nejcokorn/flysys_test/kicad/flysys_vario.kicad_sch

## KiCad design kicad/flysys_vario.kicad_sch (2026-06-08)

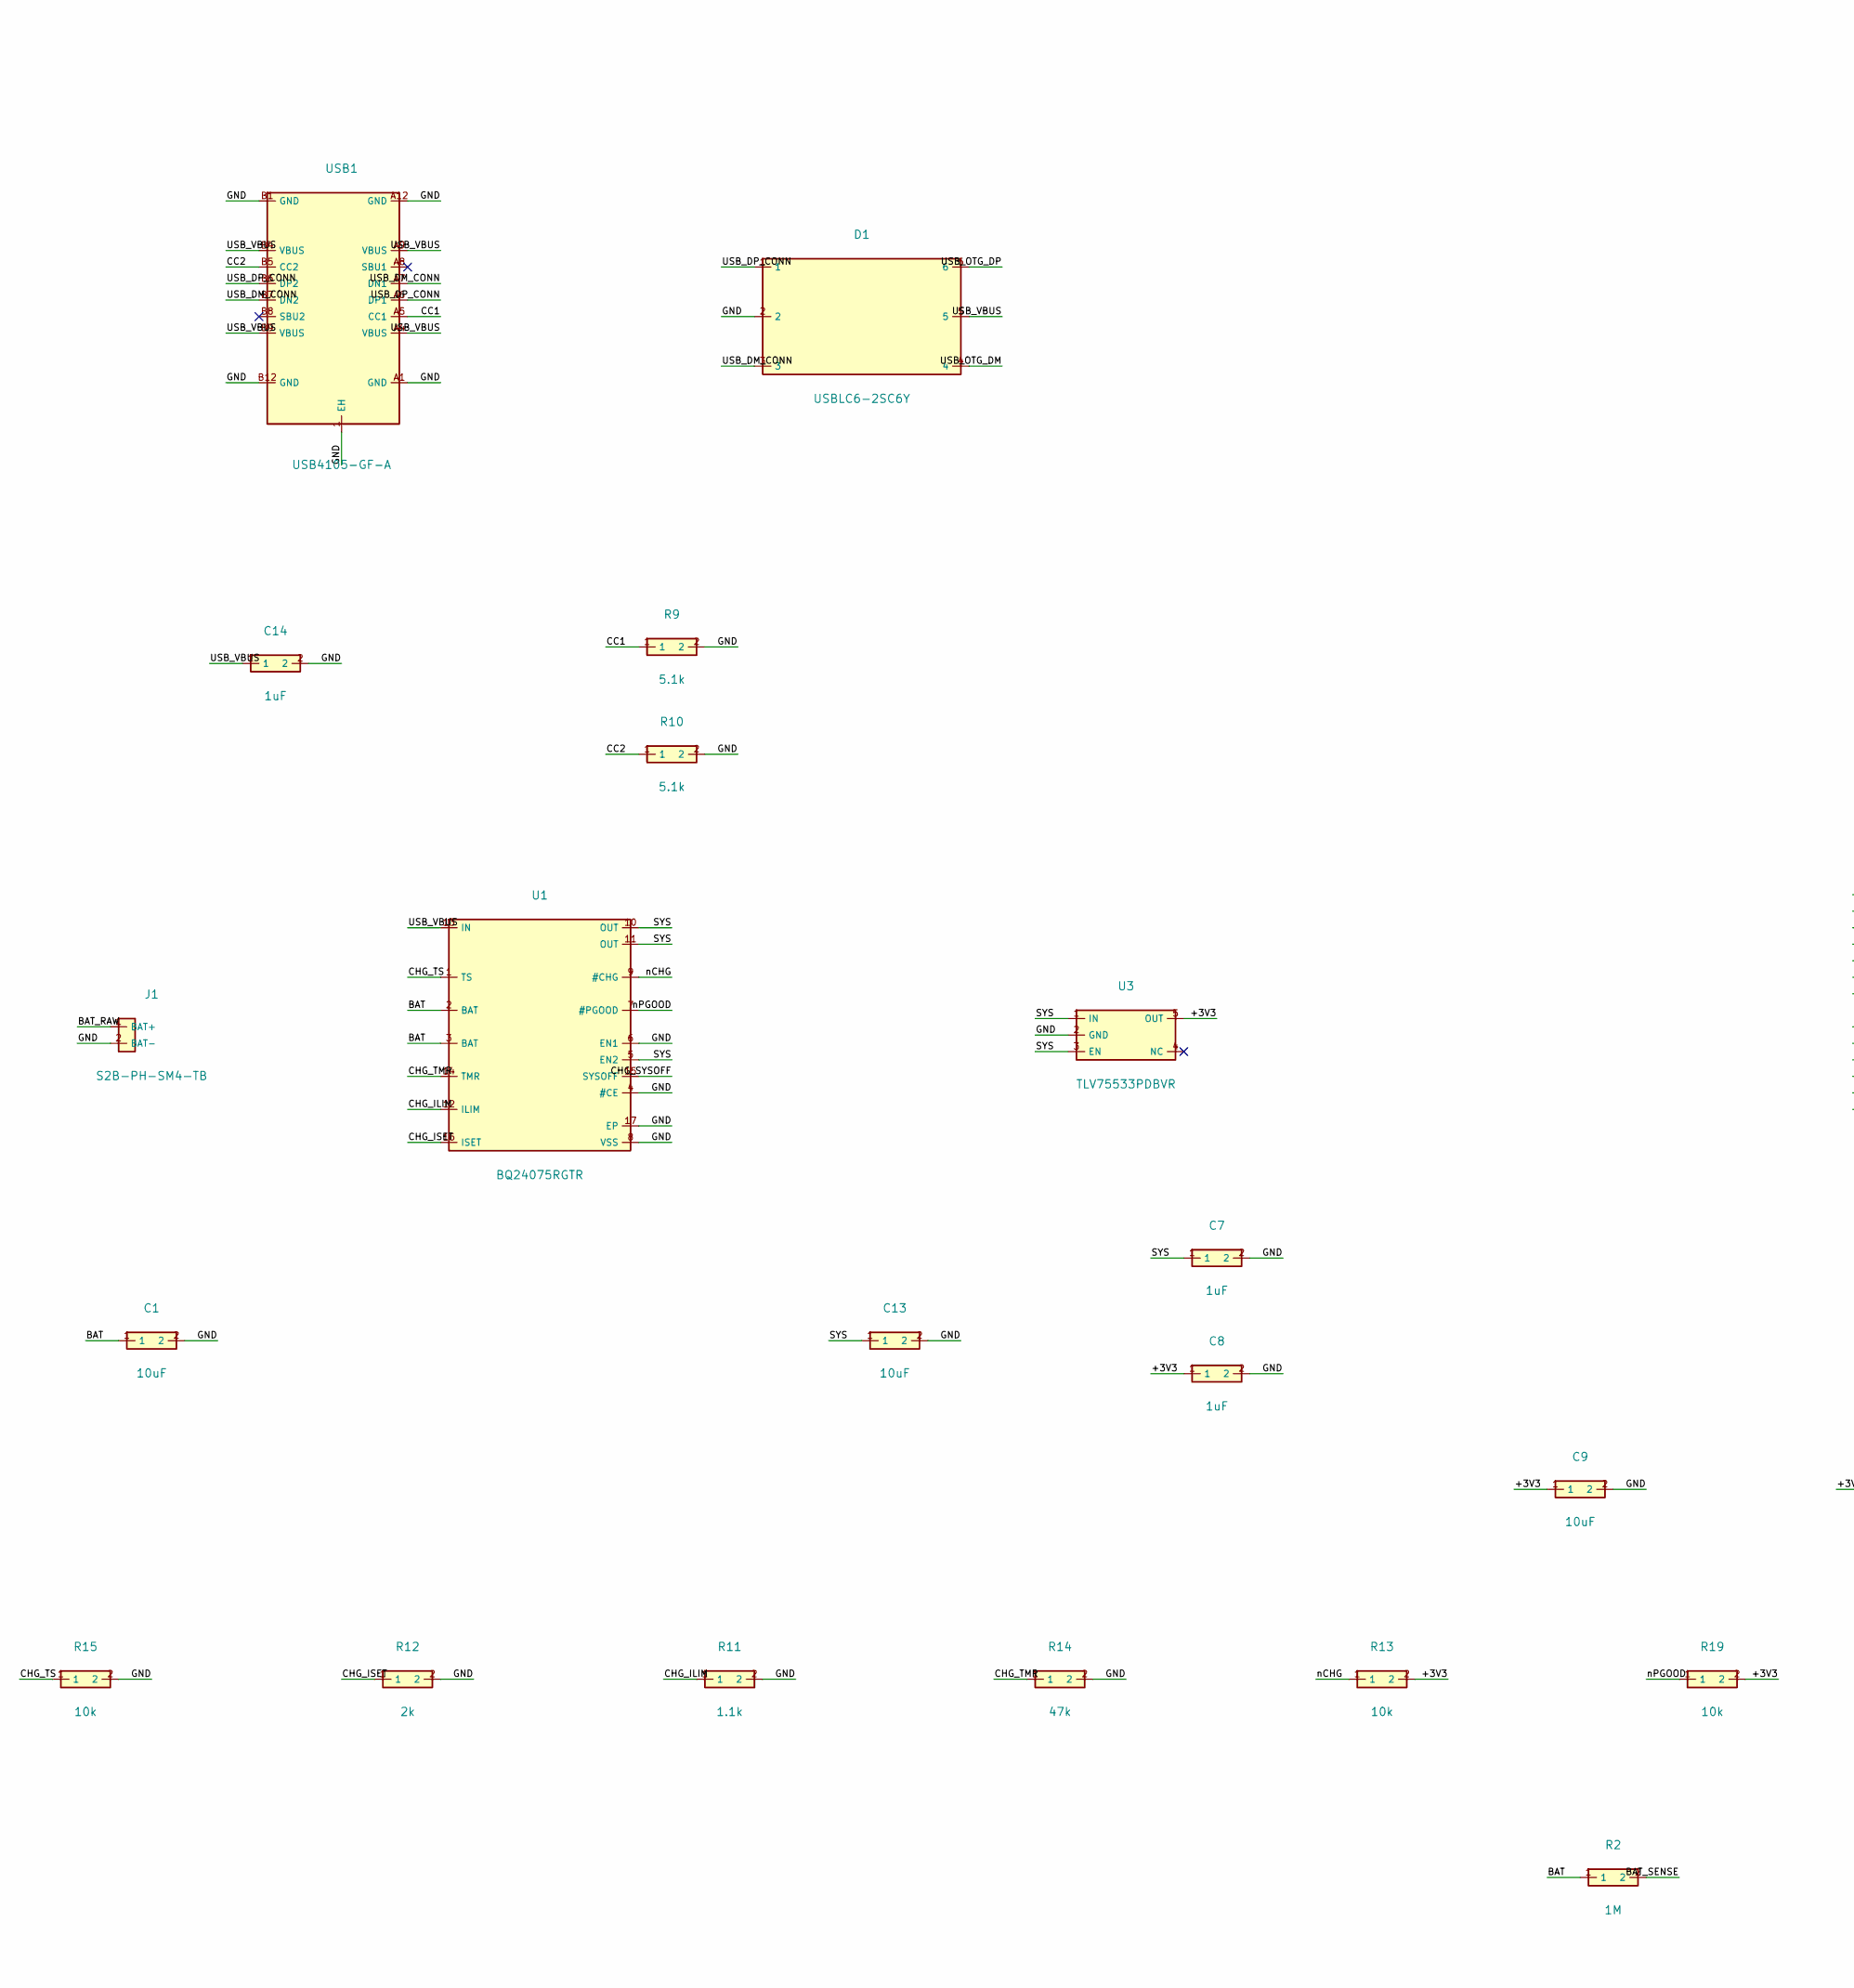
[picture p11: schematic flysys_vario.kicad_sch, part in row 1, column 1]

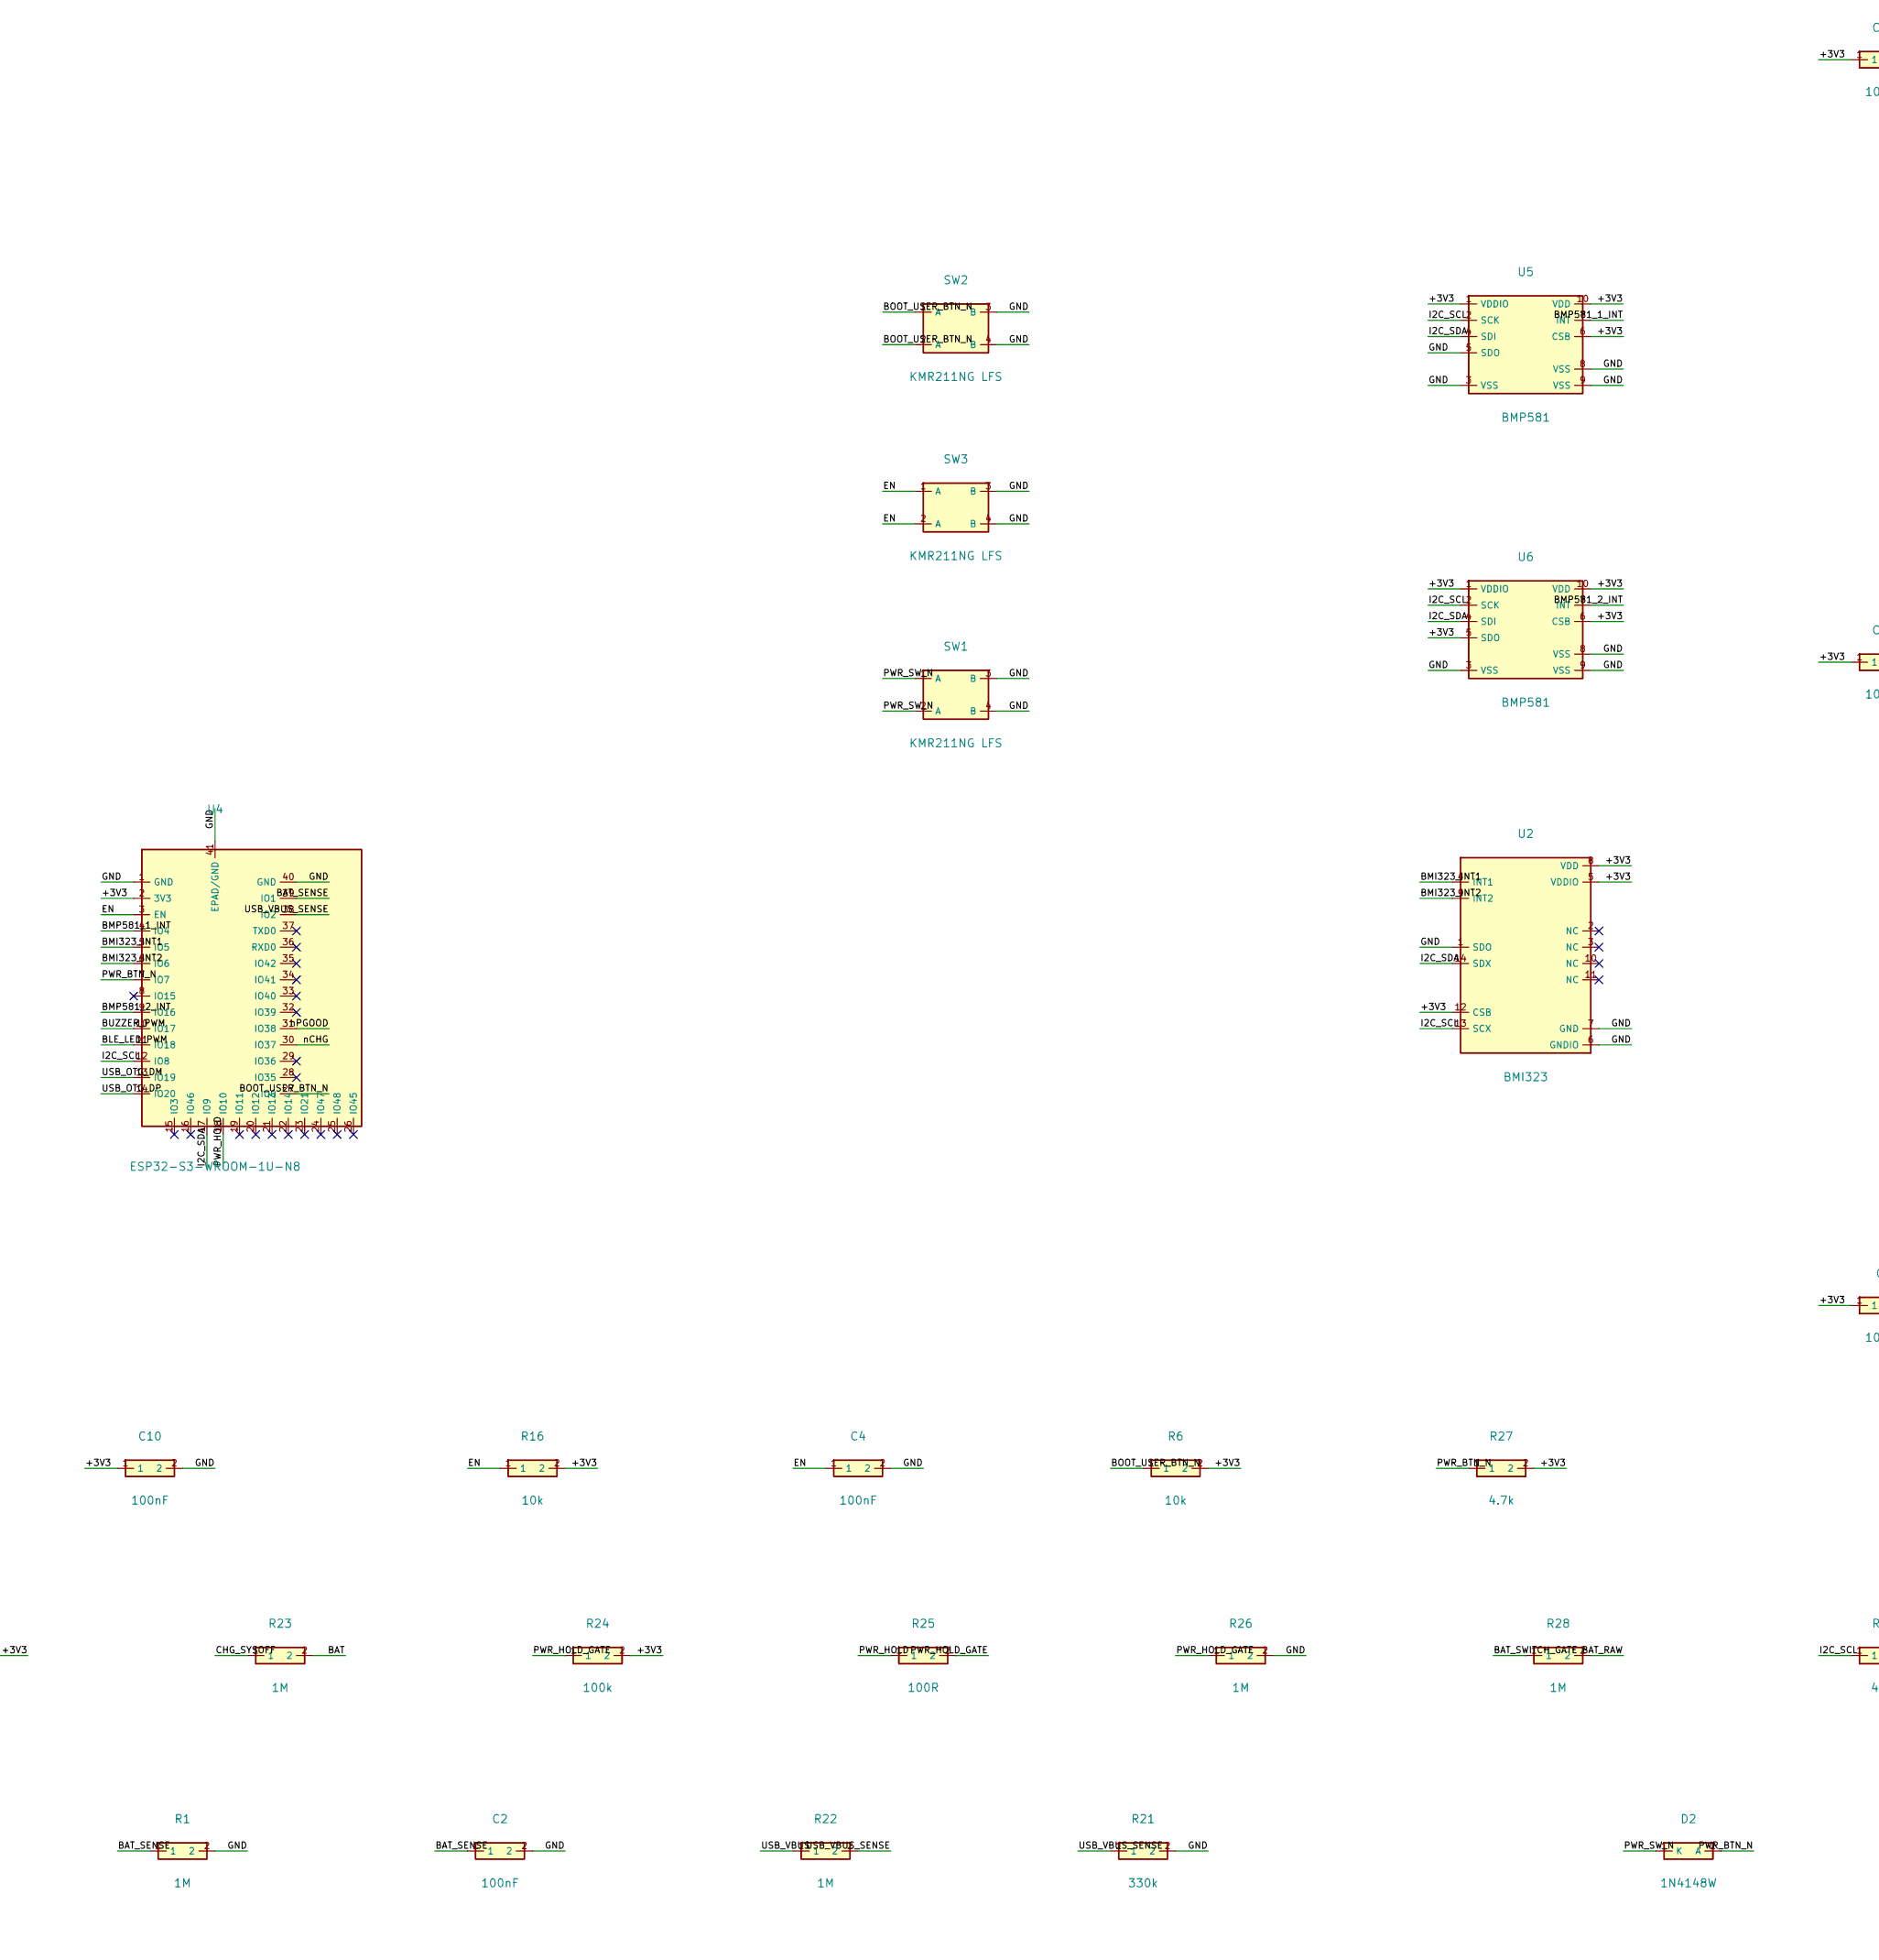
[picture p12: schematic flysys_vario.kicad_sch, part in row 1, column 2]

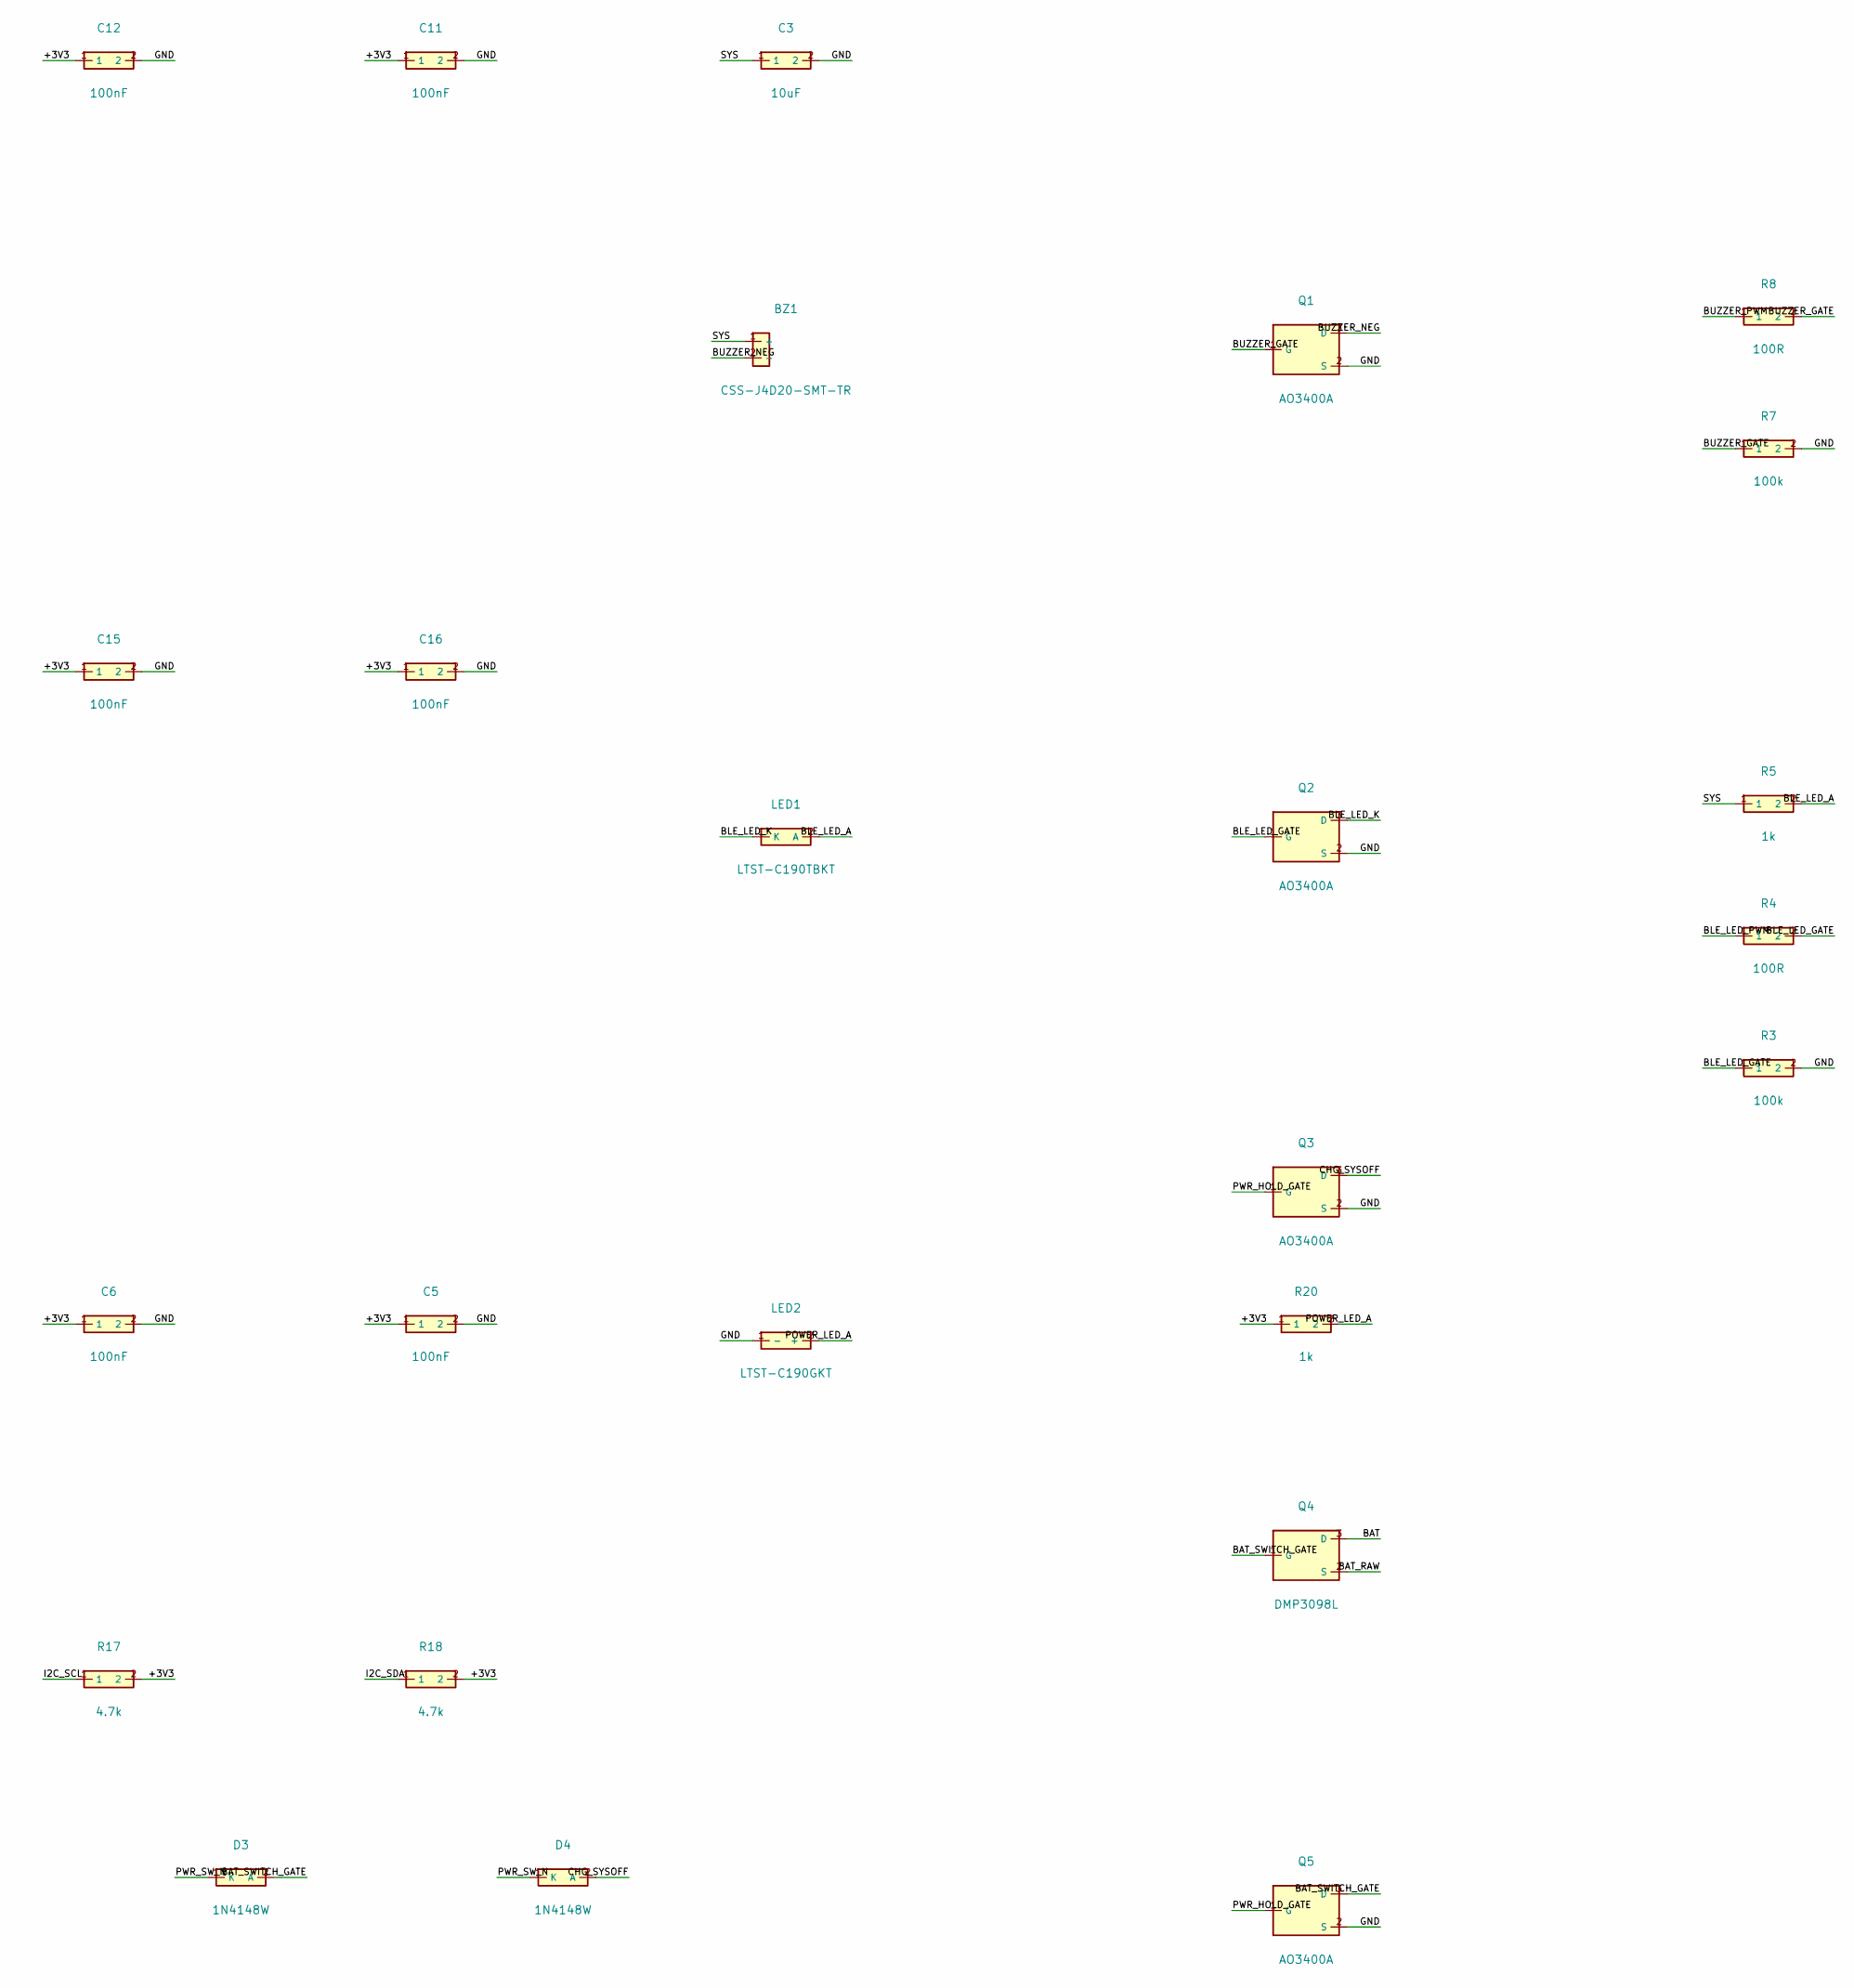
[picture p13: schematic flysys_vario.kicad_sch, part in row 1, column 3]

Parts:
BZ1: CSS-J4D20-SMT-TR; MPN CSS-J4D20-SMT-TR; DigiKey Part Number 102-1198-1-ND
C1, C3, C9, C13: 10uF; C0603; MPN CL10A106KP8NNNC; DigiKey Part Number 1276-1192-1-ND
C2, C4, C5, C6, C10, C11, C12, C15, C16: 100nF; C0603; MPN CC0603KRX7R9BB104; DigiKey Part Number 311-1344-1-ND
C7, C8, C14: 1uF; C0603; MPN CL10A105KB8NNNC; DigiKey Part Number 1276-1860-1-ND
D1: USBLC6-2SC6Y; SOT-23-6_L2.9-W1.6-P0.95-LS2.8-BL; MPN USBLC6-2SC6Y; DigiKey Part Number 497-11882-1-ND
D2, D3, D4: 1N4148W; MPN 1N4148W-7-F; DigiKey Part Number 1N4148W-FDICT-ND
J1: S2B-PH-SM4-TB; MPN S2B-PH-SM4-TB; DigiKey Part Number 455-S2B-PH-SM4-TBCT-ND
LED1: LTST-C190TBKT; LED0603-RD; MPN LTST-C190TBKT; DigiKey Part Number 160-1646-1-ND
LED2: LTST-C190GKT; LED0603-RD; MPN LTST-C190GKT; DigiKey Part Number 160-LTST-C190GKTCT-ND
Q1, Q2, Q3, Q5: AO3400A; MPN AO3400A; DigiKey Part Number 785-1000-1-ND
Q4: DMP3098L; MPN DMP3098L-7; DigiKey Part Number DMP3098LDICT-ND
R1, R2, R22, R23, R26, R28: 1M; R0603; MPN RC0603FR-071ML; DigiKey Part Number 311-1.00MHRCT-ND
R3, R7, R24: 100k; R0603; MPN RC0603FR-07100KL; DigiKey Part Number 311-100KHRCT-ND
R4, R8, R25: 100R; R0603; MPN RC0603FR-07100RL; DigiKey Part Number 311-100HRCT-ND
R5, R20: 1k; R0603; MPN RC0603FR-071KL; DigiKey Part Number 311-1.00KHRCT-ND
R6, R13, R15, R16, R19: 10k; R0603; MPN RC0603FR-0710KL; DigiKey Part Number 311-10.0KHRCT-ND
R9, R10: 5.1k; R0603; MPN RC0603FR-075K1L; DigiKey Part Number 311-5.10KHRCT-ND
R11: 1.1k; R0603; MPN RC0603FR-071K1L; DigiKey Part Number 311-1.10KHRCT-ND
R12: 2k; R0603; MPN RC0603FR-072KL; DigiKey Part Number 311-2.00KHRCT-ND
R14: 47k; R0603; MPN RC0603FR-0747KL; DigiKey Part Number 311-47.0KHRCT-ND
R17, R18, R27: 4.7k; R0603; MPN RC0603FR-074K7L; DigiKey Part Number 311-4.70KHRCT-ND
R21: 330k; R0603; MPN RC0603FR-07330KL; DigiKey Part Number 311-330KHRCT-ND
SW1: KMR211NG LFS; KMR211NG_LFS; MPN KMR211NG LFS; DigiKey Part Number CKN10243CT-ND
SW2: KMR211NG LFS; KMR211NG_LFS_BOOT; MPN KMR211NG LFS; DigiKey Part Number CKN10243CT-ND
SW3: KMR211NG LFS; KMR211NG_LFS_RST; MPN KMR211NG LFS; DigiKey Part Number CKN10243CT-ND
U1: BQ24075RGTR; QFN-16_L3.0-W3.0-P0.50-TL-EP1.7; MPN BQ24075RGTR; DigiKey Part Number 296-38874-1-ND
U2: BMI323; LGA-14_L3.0-W2.5-P0.50-TL_QMI8658A; MPN BMI323; DigiKey Part Number 828-BMI323CT-ND
U3: TLV75533PDBVR; SOT-23-5_L3.0-W1.7-P0.95-LS2.8-BR; MPN TLV75533PDBVR; DigiKey Part Number 296-50411-1-ND
U4: ESP32-S3-WROOM-1U-N8; MPN ESP32-S3-WROOM-1U-N8; DigiKey Part Number 1965-ESP32-S3-WROOM-1U-N8CT-ND
U5, U6: BMP581; BMP581_LGA10_2x2mm; MPN BMP581; DigiKey Part Number 828-BMP581CT-ND
USB1: USB4105-GF-A; TYPE-C-SMD_SBC-160S1A-20-S412; MPN USB4105-GF-A; DigiKey Part Number 2073-USB4105-GF-ACT-ND

Connections:
+3V3: C5.1, C6.1, C8.1, C9.1, C10.1, C11.1, C12.1, C15.1, C16.1, R6.2, R13.2, R16.2, R17.2, R18.2, R19.2, R20.1, R24.2, R27.2, U2.5 (VDDIO), U2.8 (VDD), U2.12 (CSB), U3.5 (OUT), U4.2 (3V3), U5.1 (VDDIO), U5.6 (CSB), U5.10 (VDD), U6.1 (VDDIO), U6.5 (SDO), U6.6 (CSB), U6.10 (VDD)
BAT: C1.1, Q4.3 (D), R2.1, R23.2, U1.2 (BAT), U1.3 (BAT)
BAT_RAW: J1.1 (BAT+), Q4.2 (S), R28.2
BAT_SENSE: C2.1, R1.1, R2.2, U4.39 (IO1)
BAT_SWITCH_GATE: D3.2 (A), Q4.1 (G), Q5.3 (D), R28.1
BLE_LED_A: LED1.2 (A), R5.2
BLE_LED_GATE: Q2.1 (G), R3.1, R4.2
BLE_LED_K: LED1.1 (K), Q2.3 (D)
BLE_LED_PWM: R4.1, U4.11 (IO18)
BMI323_INT1: U2.4 (INT1), U4.5 (IO5)
BMI323_INT2: U2.9 (INT2), U4.6 (IO6)
BMP581_1_INT: U4.4 (IO4), U5.7 (INT)
BMP581_2_INT: U4.9 (IO16), U6.7 (INT)
BOOT_USER_BTN_N: R6.1, SW2.1 (A), SW2.2 (A), U4.27 (IO0)
BUZZER_GATE: Q1.1 (G), R7.1, R8.2
BUZZER_NEG: BZ1.2 (-), Q1.3 (D)
BUZZER_PWM: R8.1, U4.10 (IO17)
CC1: R9.1, USB1.A5 (CC1)
CC2: R10.1, USB1.B5 (CC2)
CHG_ILIM: R11.1, U1.12 (ILIM)
CHG_ISET: R12.1, U1.16 (ISET)
CHG_SYSOFF: D4.2 (A), Q3.3 (D), R23.1, U1.15 (SYSOFF)
CHG_TMR: R14.1, U1.14 (TMR)
CHG_TS: R15.1, U1.1 (TS)
EN: C4.1, R16.1, SW3.1 (A), SW3.2 (A), U4.3 (EN)
GND: C1.2, C2.2, C3.2, C4.2, C5.2, C6.2, C7.2, C8.2, C9.2, C10.2, C11.2, C12.2, C13.2, C14.2, C15.2, C16.2, D1.2, J1.2 (BAT-), LED2.1 (-), Q1.2 (S), Q2.2 (S), Q3.2 (S), Q5.2 (S), R1.2, R3.2, R7.2, R9.2, R10.2, R11.2, R12.2, R14.2, R15.2, R21.2, R26.2, SW1.3 (B), SW1.4 (B), SW2.3 (B), SW2.4 (B), SW3.3 (B), SW3.4 (B), U1.4 (#CE), U1.6 (EN1), U1.8 (VSS), U1.17 (EP), U2.1 (SDO), U2.6 (GNDIO), U2.7 (GND), U3.2 (GND), U4.1 (GND), U4.40 (GND), U4.41 (EPAD/GND), U5.3 (VSS), U5.5 (SDO), U5.8 (VSS), U5.9 (VSS), U6.3 (VSS), U6.8 (VSS), U6.9 (VSS), USB1.1 (EH), USB1.A1 (GND), USB1.A12 (GND), USB1.B1 (GND), USB1.B12 (GND)
I2C_SCL: R17.1, U2.13 (SCX), U4.12 (IO8), U5.2 (SCK), U6.2 (SCK)
I2C_SDA: R18.1, U2.14 (SDX), U4.17 (IO9), U5.4 (SDI), U6.4 (SDI)
POWER_LED_A: LED2.2 (+), R20.2
PWR_BTN_N: D2.2 (A), R27.1, U4.7 (IO7)
PWR_HOLD: R25.1, U4.18 (IO10)
PWR_HOLD_GATE: Q3.1 (G), Q5.1 (G), R24.1, R25.2, R26.1
PWR_SW_N: D2.1 (K), D3.1 (K), D4.1 (K), SW1.1 (A), SW1.2 (A)
SYS: BZ1.1 (+), C3.1, C7.1, C13.1, R5.1, U1.5 (EN2), U1.10 (OUT), U1.11 (OUT), U3.1 (IN), U3.3 (EN)
USB_DM_CONN: D1.3, USB1.A7 (DN1), USB1.B7 (DN2)
USB_DP_CONN: D1.1, USB1.A6 (DP1), USB1.B6 (DP2)
USB_OTG_DM: D1.4, U4.13 (IO19)
USB_OTG_DP: D1.6, U4.14 (IO20)
USB_VBUS: C14.1, D1.5, R22.1, U1.13 (IN), USB1.A4 (VBUS), USB1.A9 (VBUS), USB1.B4 (VBUS), USB1.B9 (VBUS)
USB_VBUS_SENSE: R21.1, R22.2, U4.38 (IO2)
nCHG: R13.1, U1.9 (#CHG), U4.30 (IO37)
nPGOOD: R19.1, U1.7 (#PGOOD), U4.31 (IO38)
